jbilander/PLCC-84-plug/KiCad/PLCC-84-Plug-bottom/PLCC-84-Plug-bottom.sch

## KiCad design KiCad/PLCC-84-Plug-bottom/PLCC-84-Plug-bottom.sch (2021-07-04)

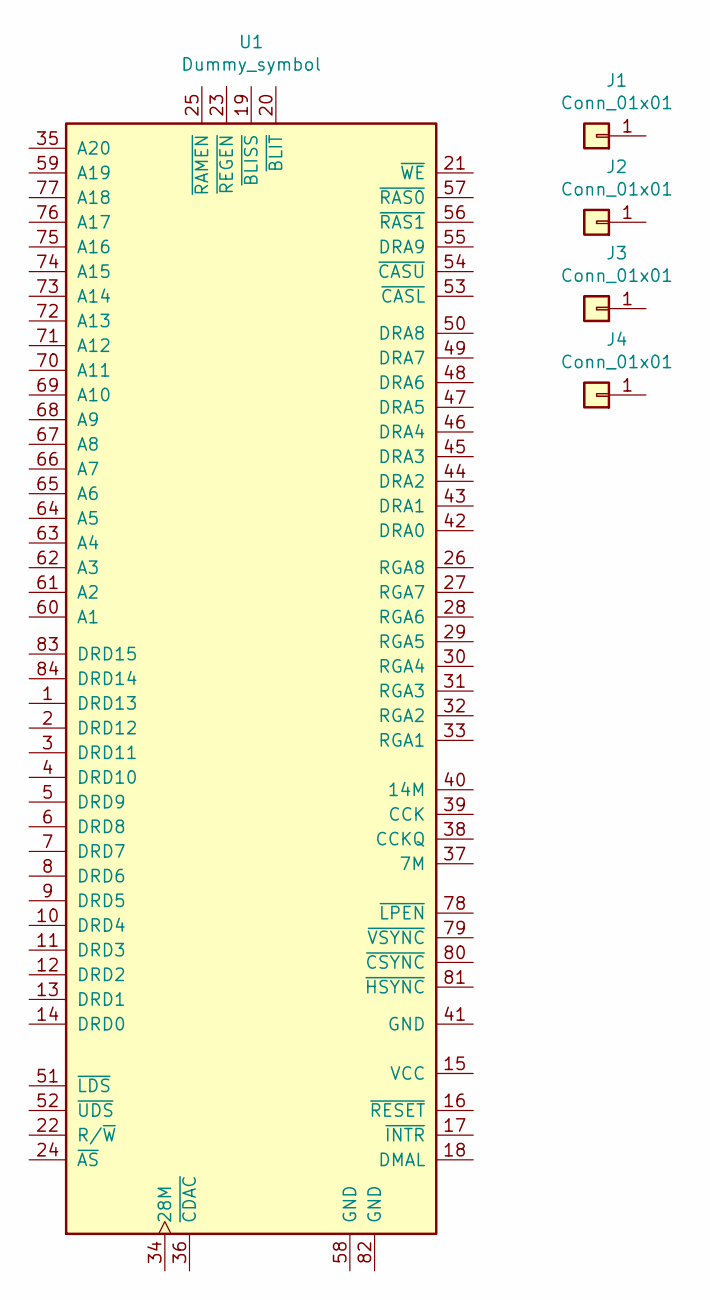
[picture p31: schematic PLCC-84-Plug-bottom.sch]

Parts:
J1, J2, J3, J4: Conn_01x01; PinHeader_1x01_P2.54mm_Vertical
U1: Dummy_symbol; PLCC-84_modded_P1.27mm
