jbilander/PLCC-84-plug/KiCad/PLCC-84-Plug-support-structure/PLCC-84-Plug-support.sch

## KiCad design KiCad/PLCC-84-Plug-support-structure/PLCC-84-Plug-support.sch (2021-07-04)

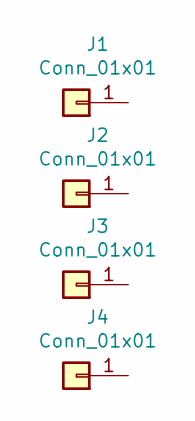
[picture p32: schematic PLCC-84-Plug-support.sch]

Parts:
J1, J2, J3, J4: Conn_01x01; PinHeader_1x01_P2.54mm_Vertical
